stevenchadburrow/AcolyteHandPICd32/tables.c

const unsigned char text_bitmap[64*96] = { 
	0x00,0x00,0x00,0x00,0x00,0x00,0x00,0x00,0x00,0x00,0x00,0x00,0x00,0x00,0x00,0x00,0x00,0x00,0x00,0x00,0x00,0x00,0x00,0x00,0x00,0x00,0x00,0x00,0x00,0x00,0x00,0x00, // 32
	0x00,0x00,0x00,0x00,0x00,0x00,0x00,0x00,0x00,0x00,0x00,0x00,0x00,0x00,0x00,0x00,0x00,0x00,0x00,0x00,0x00,0x00,0x00,0x00,0x00,0x00,0x00,0x00,0x00,0x00,0x00,0x00,
	0x00,0x00,0xFF,0xFF,0x00,0x00,0x00,0x00,0x00,0xFF,0xFF,0xFF,0xFF,0x00,0x00,0x00,0x00,0xFF,0xFF,0xFF,0xFF,0x00,0x00,0x00,0x00,0xFF,0xFF,0xFF,0xFF,0x00,0x00,0x00,
	0x00,0x00,0xFF,0xFF,0x00,0x00,0x00,0x00,0x00,0x00,0x00,0x00,0x00,0x00,0x00,0x00,0x00,0x00,0xFF,0xFF,0x00,0x00,0x00,0x00,0x00,0x00,0x00,0x00,0x00,0x00,0x00,0x00,
	0x00,0x00,0xFF,0x00,0x00,0xFF,0x00,0x00,0x00,0xFF,0x00,0x00,0xFF,0x00,0x00,0x00,0x00,0xFF,0xFF,0x00,0xFF,0xFF,0x00,0x00,0x00,0xFF,0xFF,0x00,0xFF,0xFF,0x00,0x00,
	0x00,0x00,0x00,0x00,0x00,0x00,0x00,0x00,0x00,0x00,0x00,0x00,0x00,0x00,0x00,0x00,0x00,0x00,0x00,0x00,0x00,0x00,0x00,0x00,0x00,0x00,0x00,0x00,0x00,0x00,0x00,0x00,
	0x00,0xFF,0xFF,0x00,0xFF,0xFF,0x00,0x00,0xFF,0xFF,0xFF,0xFF,0xFF,0xFF,0xFF,0x00,0x00,0xFF,0xFF,0x00,0xFF,0xFF,0x00,0x00,0x00,0xFF,0xFF,0x00,0xFF,0xFF,0x00,0x00,
	0x00,0xFF,0xFF,0x00,0xFF,0xFF,0x00,0x00,0xFF,0xFF,0xFF,0xFF,0xFF,0xFF,0xFF,0x00,0x00,0xFF,0xFF,0x00,0xFF,0xFF,0x00,0x00,0x00,0x00,0x00,0x00,0x00,0x00,0x00,0x00,
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
};
	
const unsigned char gb_preset[15][12] = {
	{0x70,0x4D,0x29,0x28,0x70,0x4D,0x29,0x28,0x70,0x4D,0x29,0x28}, // gb original
	{0xDA,0x91,0x48,0x00,0xDA,0x91,0x48,0x00,0xDA,0x91,0x48,0x00}, // gb pocket
	{0x16,0x11,0x0D,0x08,0x16,0x11,0x0D,0x08,0x16,0x11,0x0D,0x08}, // gb light
	{0xFF,0x5C,0xE8,0x00,0xFF,0x5C,0xE8,0x00,0xFF,0x5C,0xE8,0x00},
	{0xFF,0xFC,0xE0,0x00,0xFF,0xFC,0xE0,0x00,0xFF,0xFC,0xE0,0x00},
	{0xFF,0xF5,0x84,0x00,0xFF,0xF5,0x84,0x00,0xFF,0xF5,0x84,0x00},
	{0x00,0x12,0xF8,0xFF,0x00,0x12,0xF8,0xFF,0x00,0x12,0xF8,0xFF},
	{0xFF,0xB6,0x49,0x00,0xFF,0xB6,0x49,0x00,0xFF,0xB6,0x49,0x00},
	{0xFE,0xF2,0x93,0x00,0xFE,0xF2,0x93,0x00,0xFE,0xF2,0x93,0x00},
	{0xFF,0xF5,0x84,0x00,0xFF,0xF5,0x84,0x00,0xFF,0xD2,0x8C,0x44},
	{0xFF,0xF2,0x84,0x00,0xFF,0xF2,0x84,0x00,0xFF,0x7C,0x0F,0x00},
	{0xFF,0xF2,0x84,0x00,0xFF,0xF5,0x84,0x00,0xFF,0x93,0x4A,0x00},
	{0xFF,0x7C,0x10,0x00,0xFF,0x77,0x03,0x00,0xFF,0xF2,0x84,0x00},
	{0xFF,0xF2,0x84,0x00,0xFF,0x7C,0x10,0x00,0xFF,0x77,0x03,0x00},
	{0xFF,0x77,0x03,0x00,0xFF,0x7C,0x10,0x00,0xFF,0xFC,0x68,0x00},
};
